petrilakm/Sablik_kolejova_deska/IO_master/doc/IO_master_nano_doc.pdf

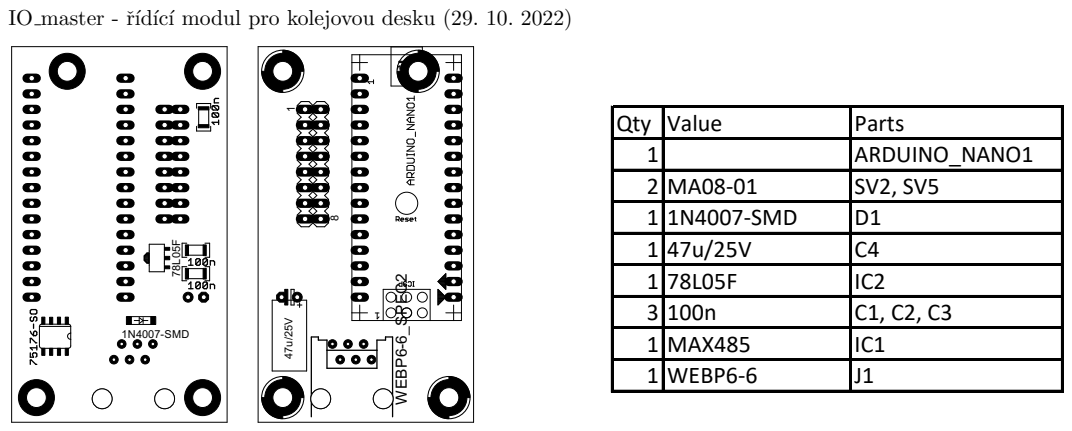
[picture p1: page 1]
1N4007-SMD; 47u/25V WEBP6-6_SPEC2

IO master - ˇr´ıd´ıc´ı modul pro kolejovou desku (29. 10. 2022)

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
