petrilakm/Sablik_kolejova_deska/IO_master/doc/IO_master_nano_pb.pdf

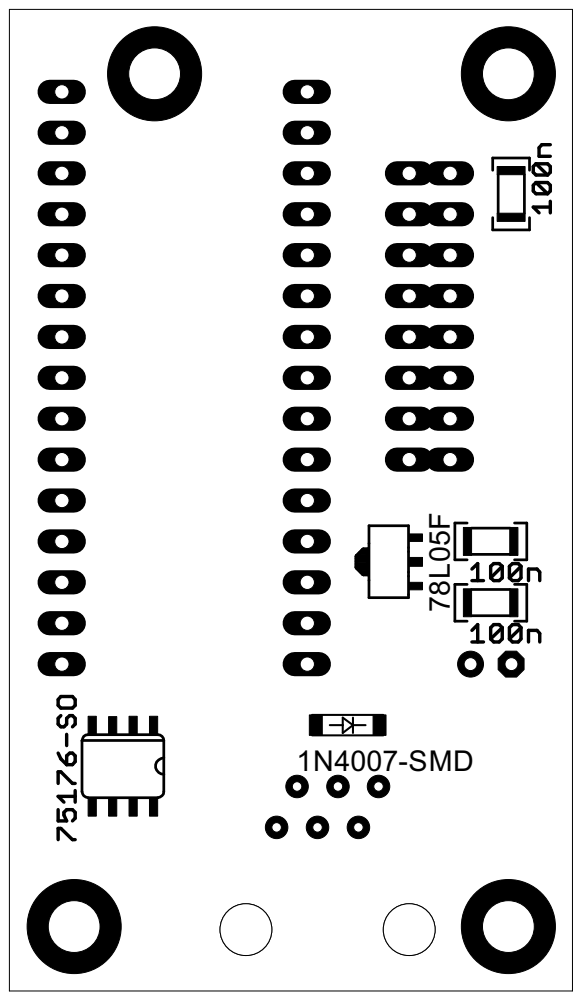
[picture p12: page 1]
