petrilakm/Sablik_kolejova_deska/IO_master/doc/IO_master_nano_pt.pdf

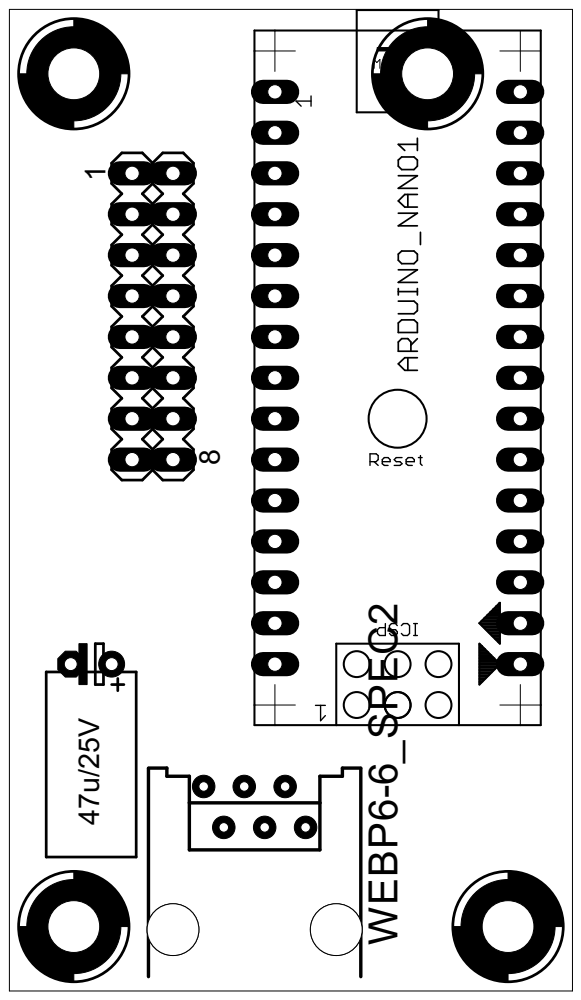
[picture p13: page 1]
