petrilakm/Sablik_kolejova_deska/IO_master/doc/IO_master_nano_sch.pdf

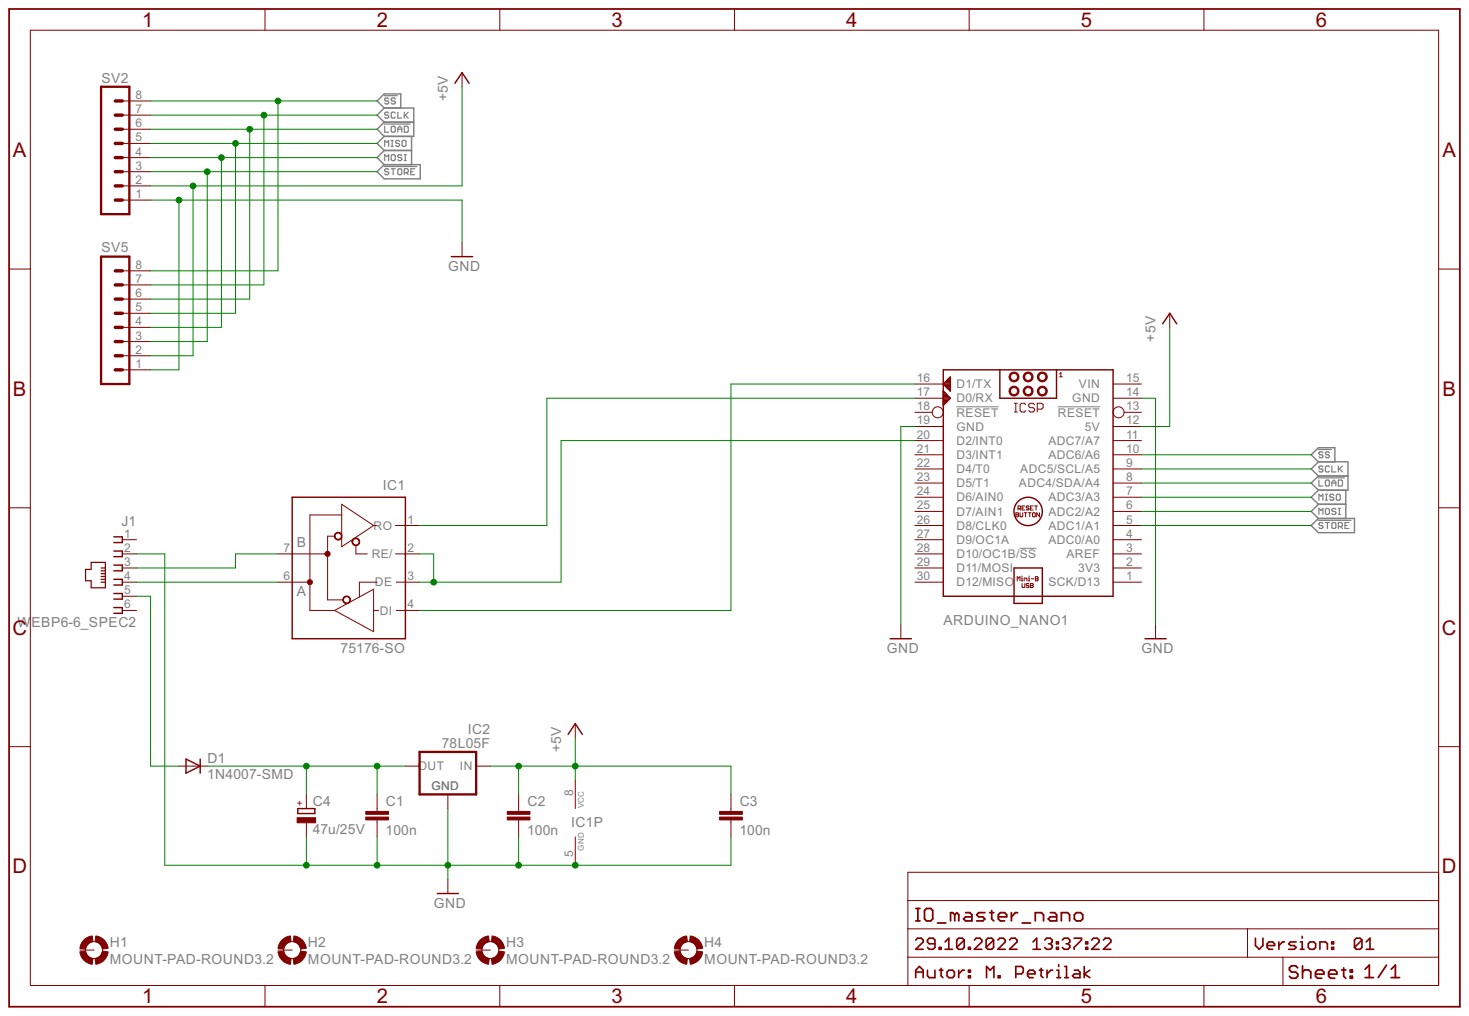
[picture p14: page 1]

20 | 10 ADC7/A7 9 ADC6/A6 8 ADC5/SCL/A5 7 ADC4/SDA/A4 6 ADC3/A3 5 ADC2/A2 4 ADC1/A1 3 ADC0/A0 2 AREF
21
