petrilakm/Sablik_kolejova_deska/IO_SPI/doc/kolejova_deska_doc.pdf

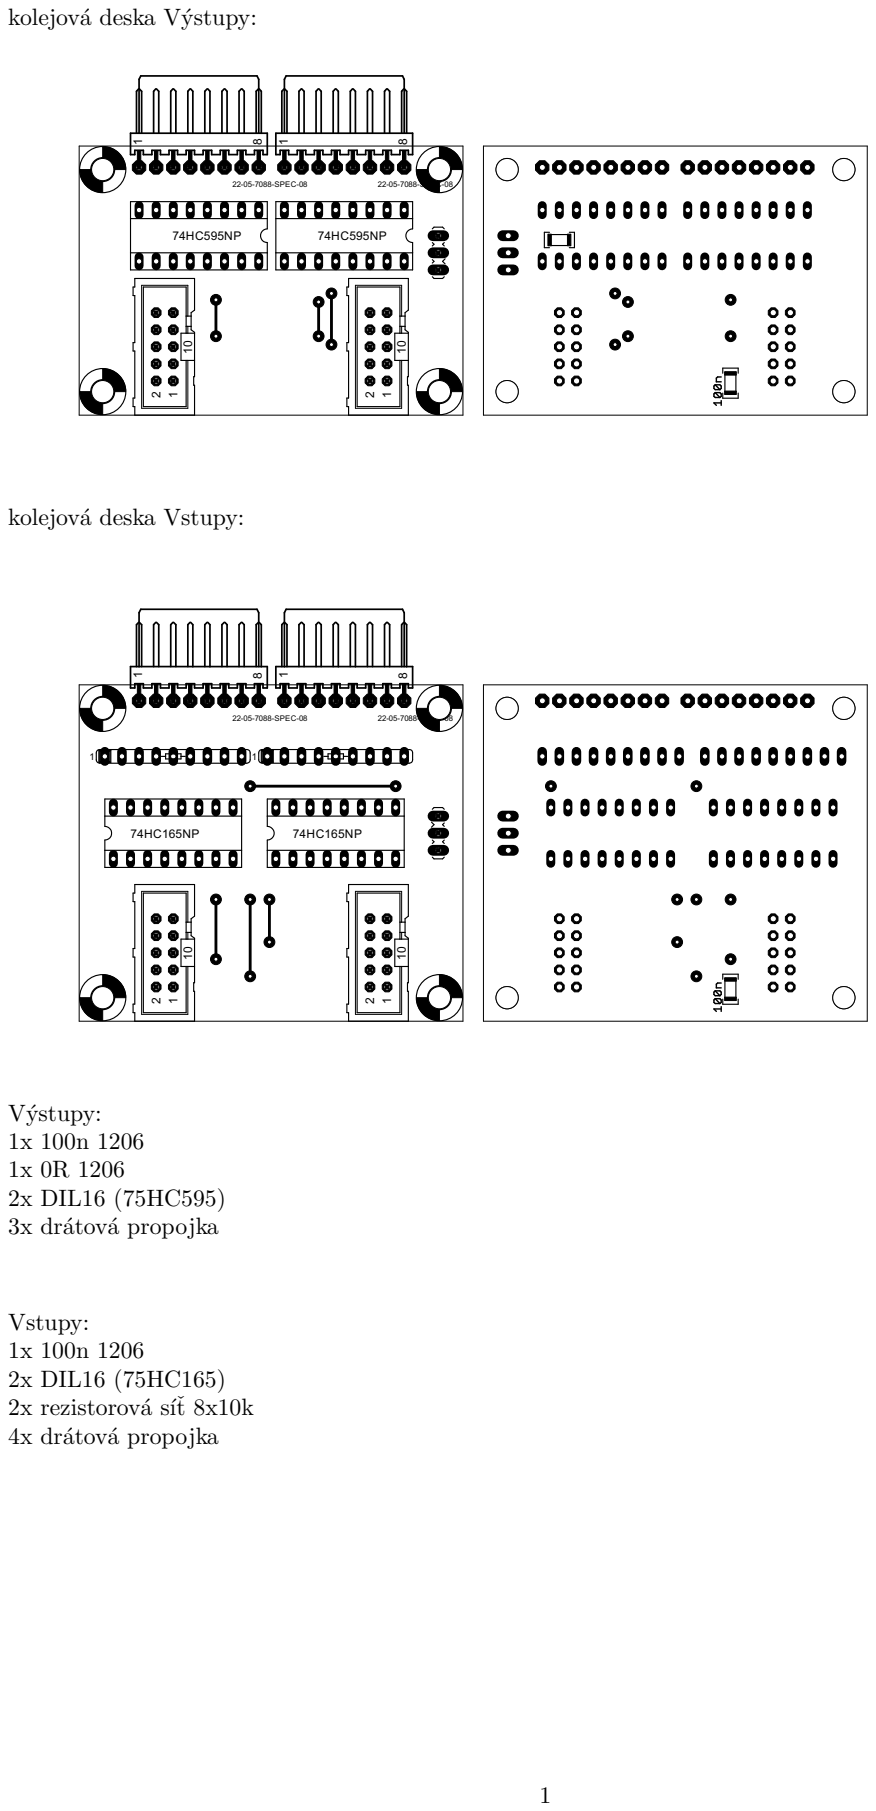
[picture p15: page 1]
22-05-7088-SPEC-08; V´ystupy: 1x 100n 1206 1x 0R 1206 2x DIL16 (75HC595) 3x dr´atov´a propojka; Vstupy: 1x 100n 1206 2x DIL16 (75HC165) 2x rezistorov´a s´ıˇt 8x10k; 4x dr´atov´a propojka

kolejov´a deska V´ystupy:

kolejov´a deska Vstupy:
