petrilakm/Sablik_kolejova_deska/IO_SPI/doc/RPi_SPI_inputs_v04_brd.pdf

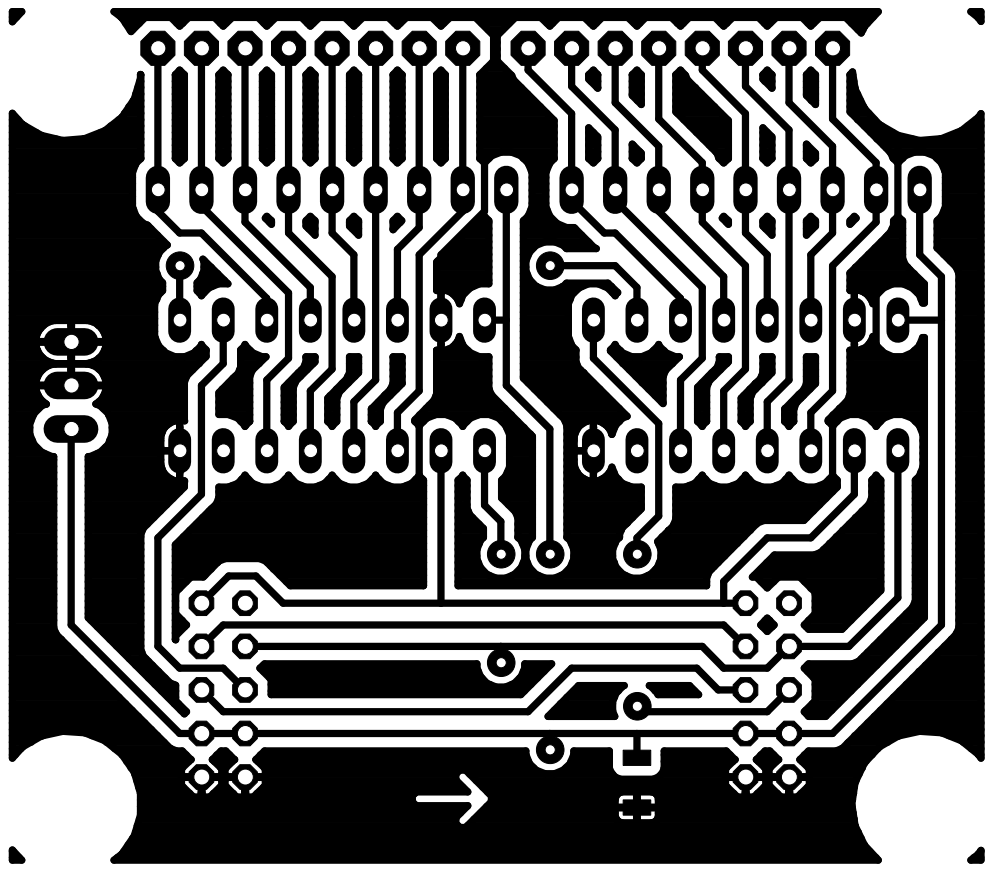
[picture p16: page 1]
