petrilakm/Sablik_kolejova_deska/IO_SPI/doc/RPi_SPI_inputs_v04_pb.pdf

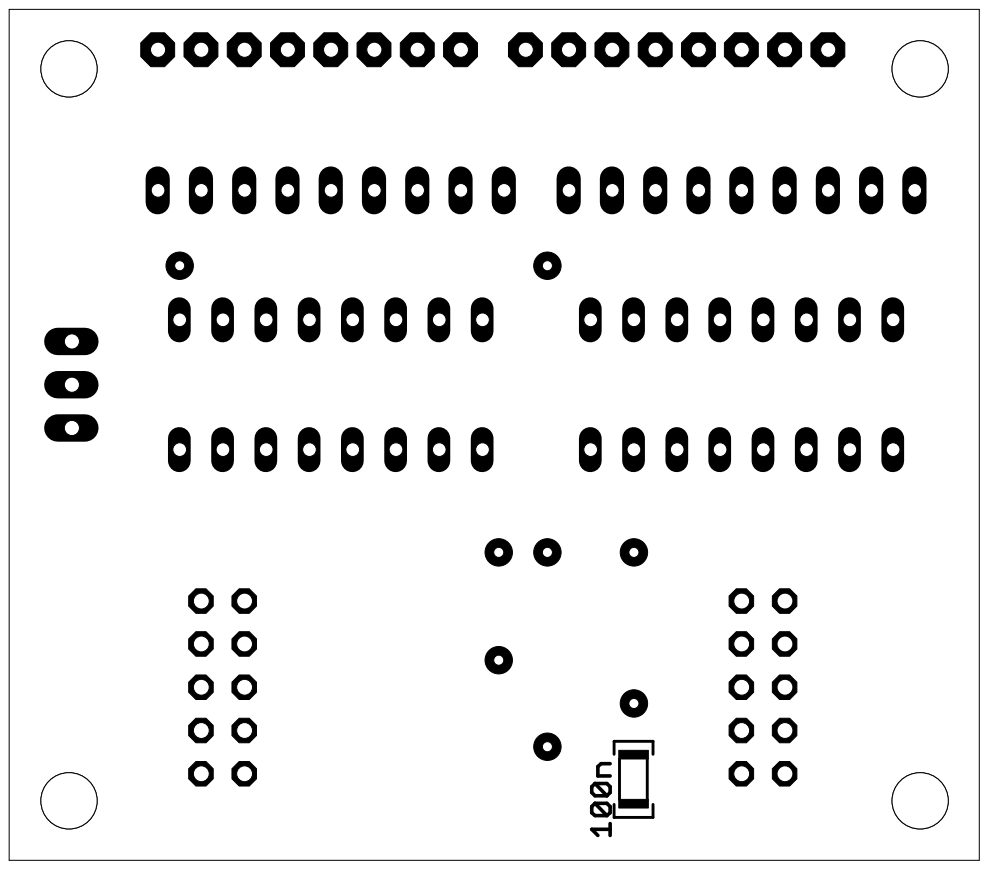
[picture p17: page 1]
