petrilakm/Sablik_kolejova_deska/IO_SPI/doc/RPi_SPI_inputs_v04_pt.pdf

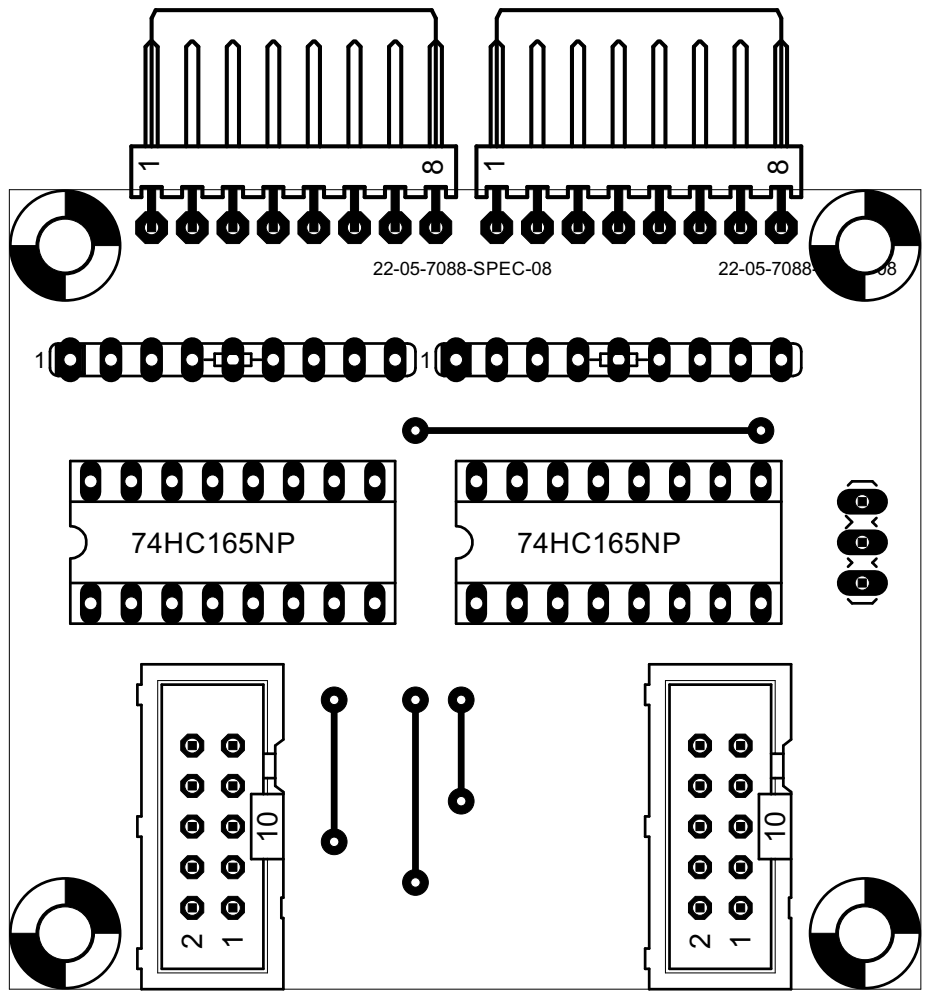
[picture p18: page 1]
