petrilakm/Sablik_kolejova_deska/IO_SPI/doc/RPi_SPI_outputs_v04.pdf

# kolejov´a deska V´ystupy:

74HC595NP | 74HC595NP

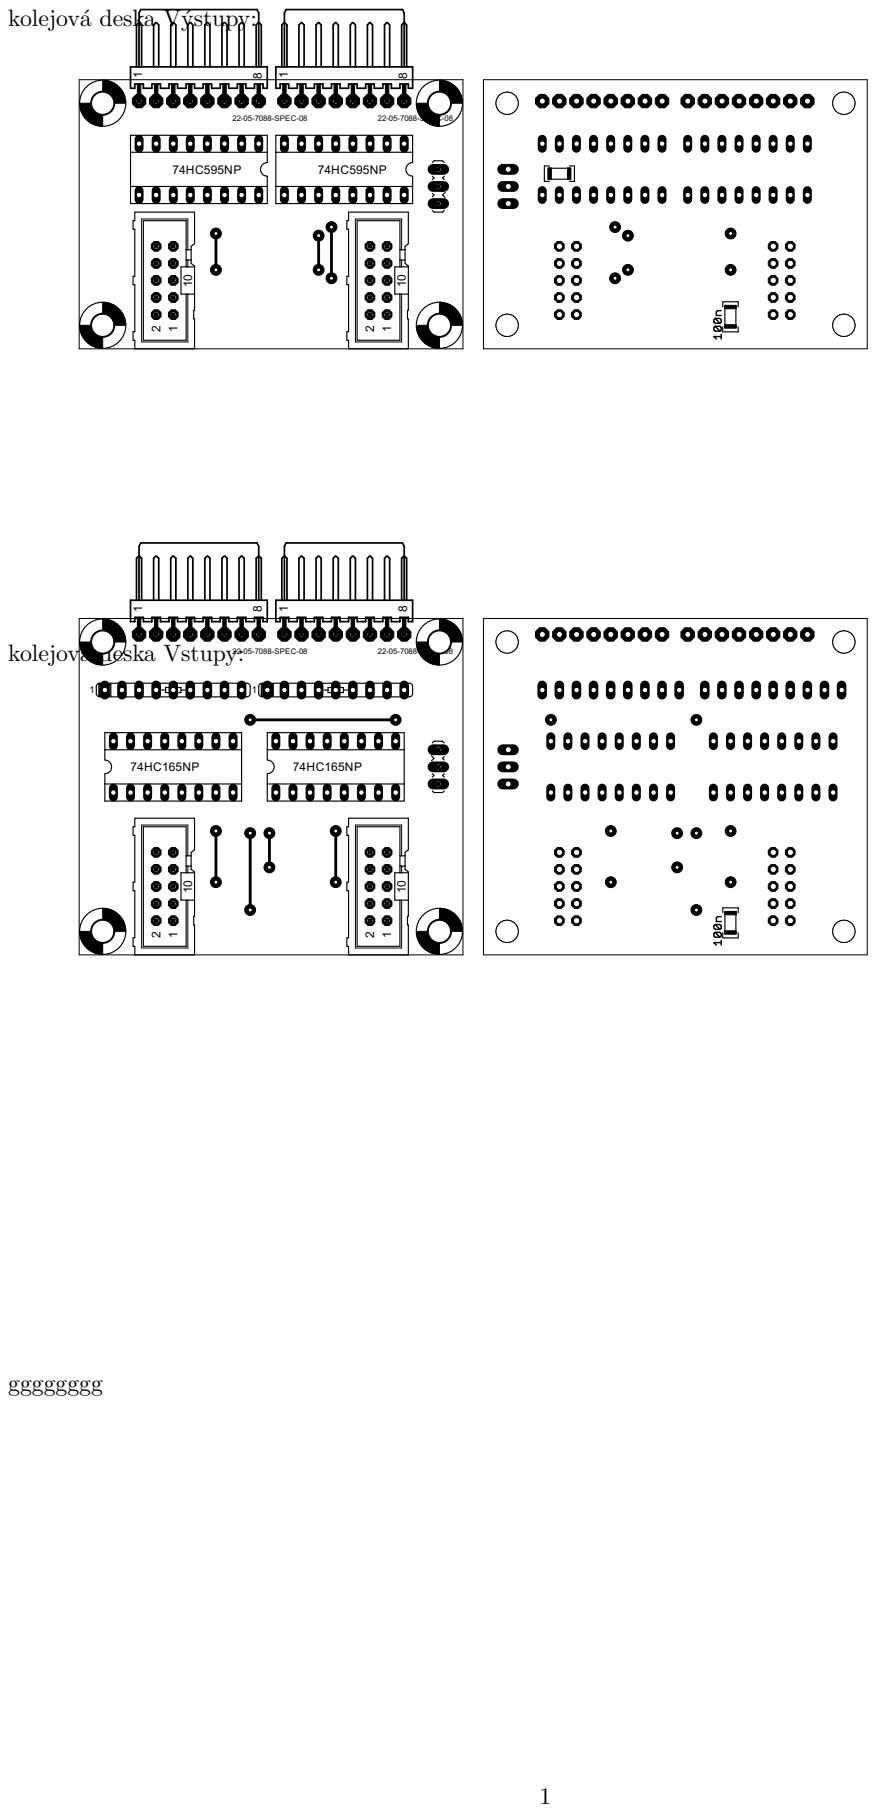
[picture p19: page 1]
22-05-7088-SPEC-08; gggggggg

kolejov´a deska Vstupy:
