petrilakm/Sablik_kolejova_deska/IO_SPI/doc/RPi_SPI_outputs_v04_brd.pdf

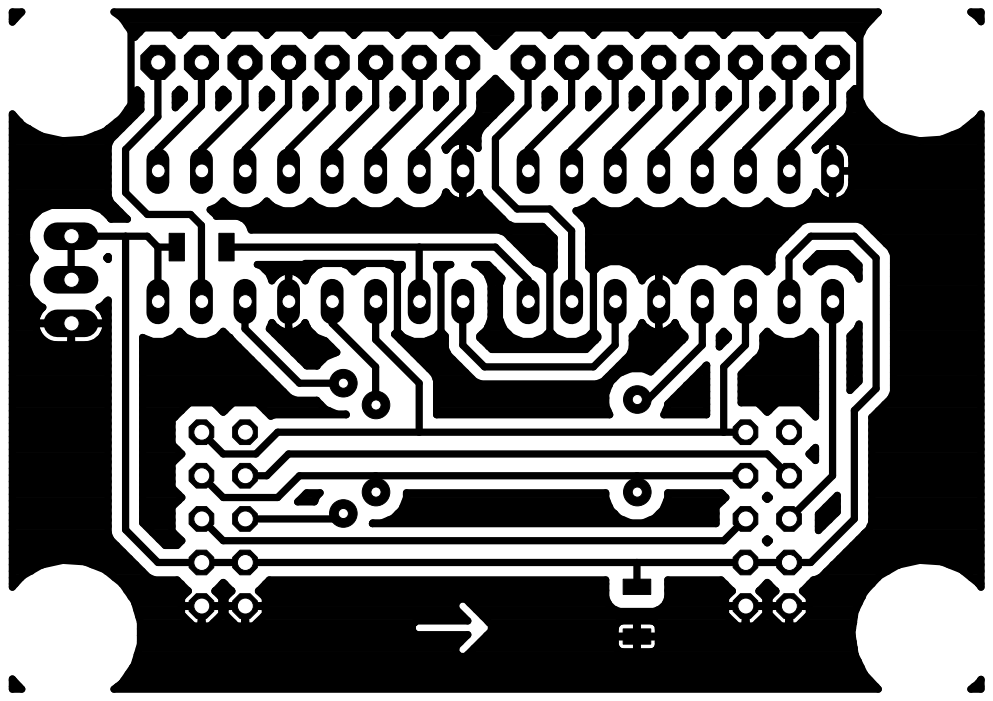
[picture p20: page 1]
