petrilakm/Sablik_kolejova_deska/IO_SPI/doc/RPi_SPI_outputs_v04_pb.pdf

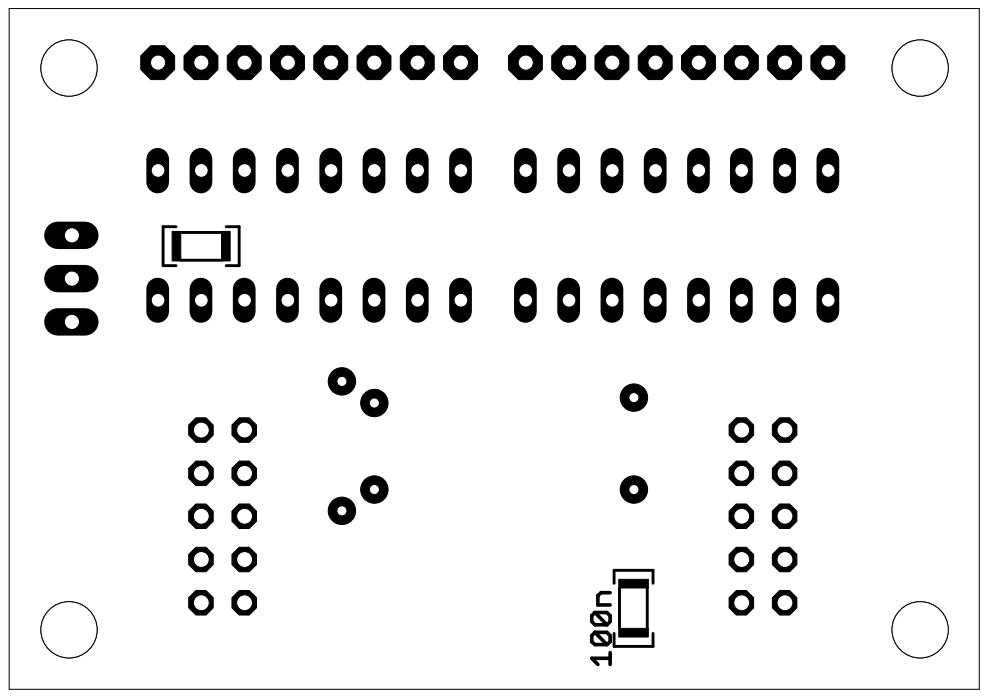
[picture p21: page 1]
