petrilakm/Sablik_kolejova_deska/IO_SPI/doc/RPi_SPI_outputs_v04_pt.pdf

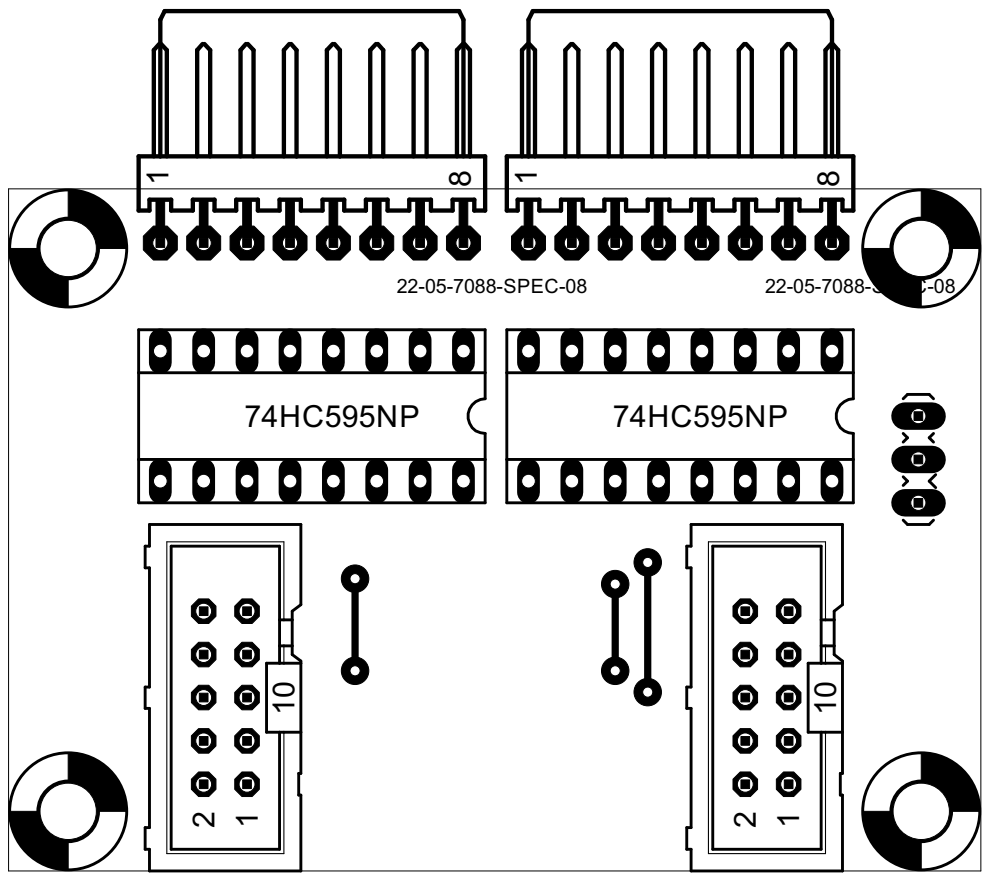
[picture p22: page 1]
