petrilakm/Sablik_kolejova_deska/IO_SPI/doc/RPi_SPI_outputs_v04_sch.pdf

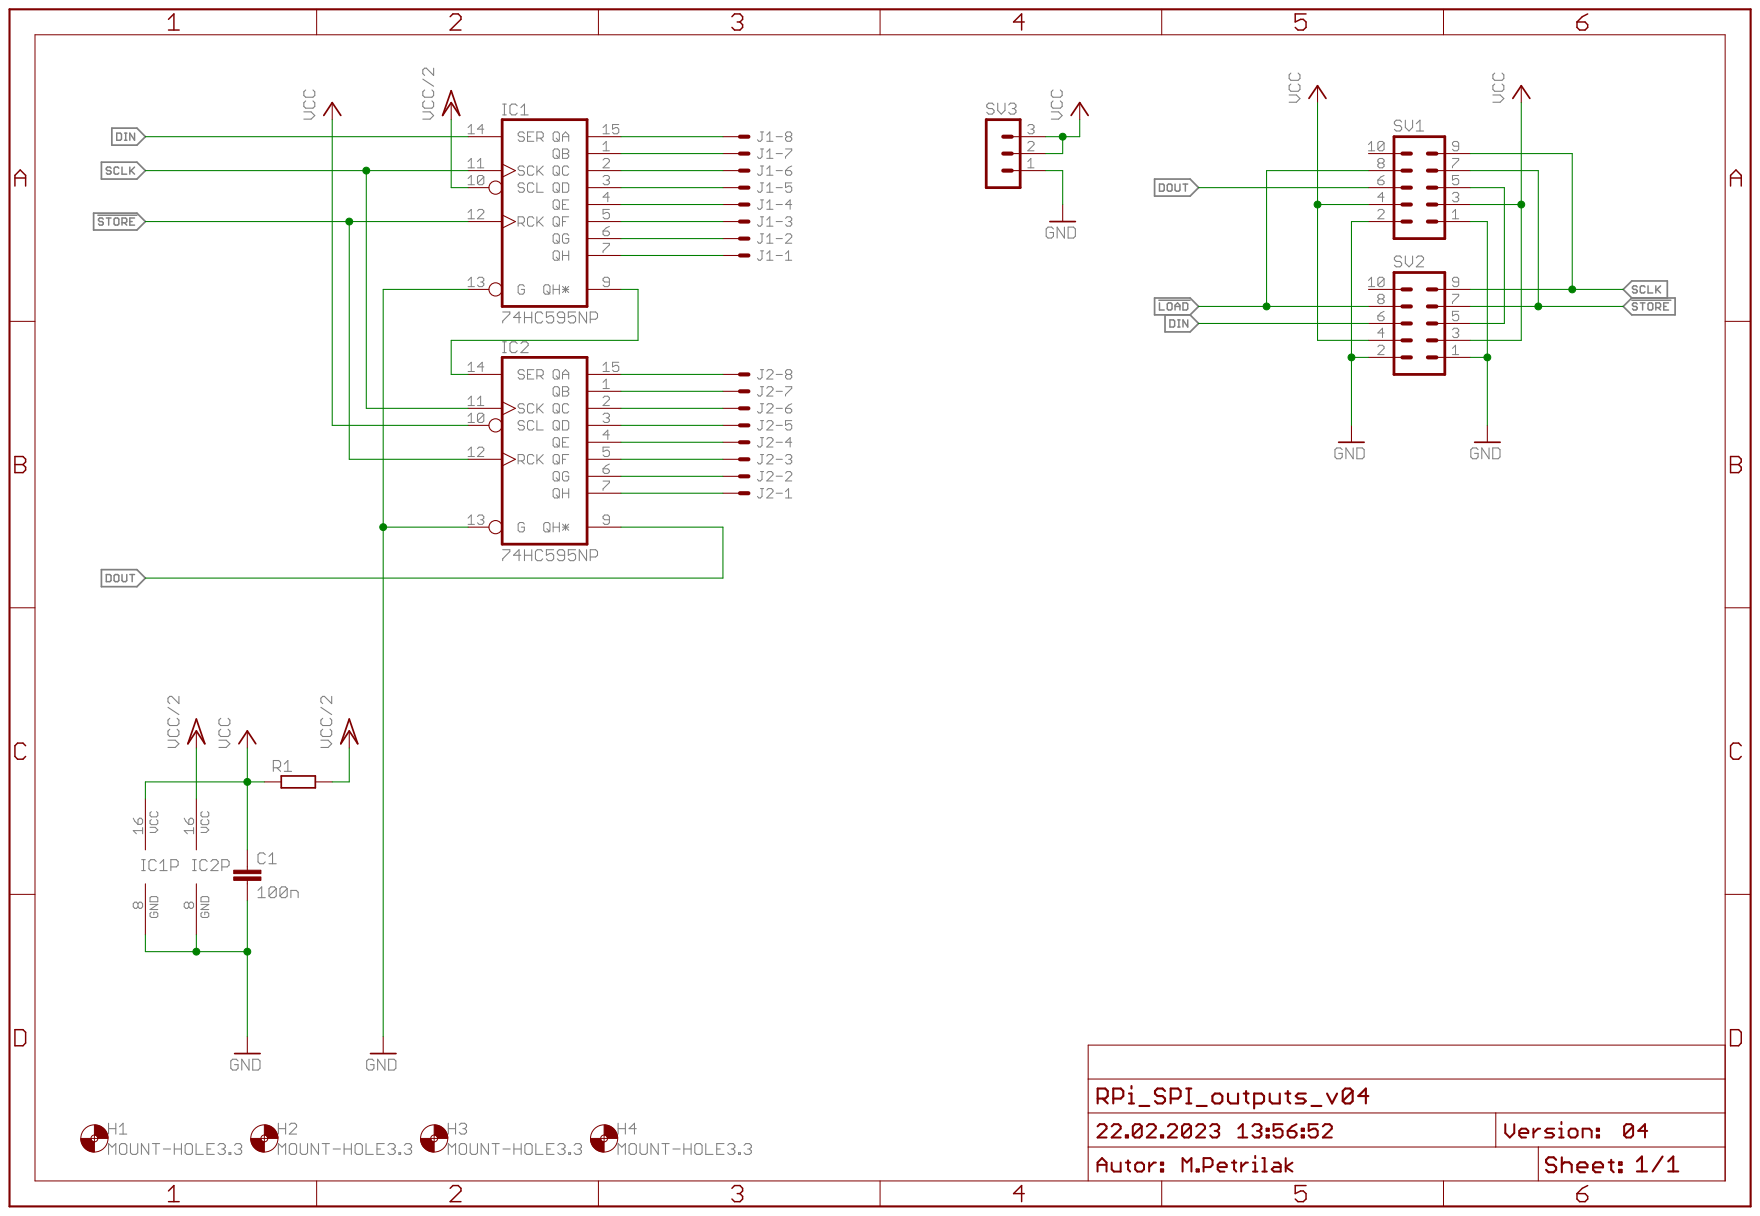
[picture p23: page 1]
